EmreErbas/Meropeidae_Horologium/Documents/Notes/Pictures/ESP32-S3-Feather-Lyt.png

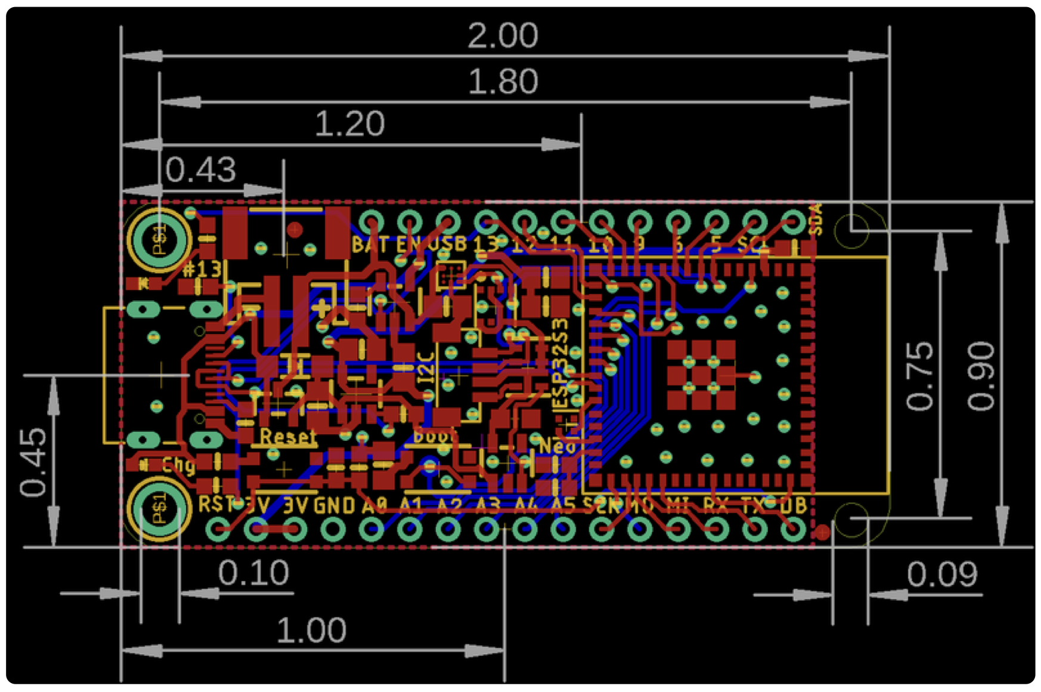
Documents/Notes/Pictures/ESP32-S3-Feather-Lyt.png
