EmreErbas/Meropeidae_Horologium/Documents/Notes/Pictures/Panel-Port-Down.png

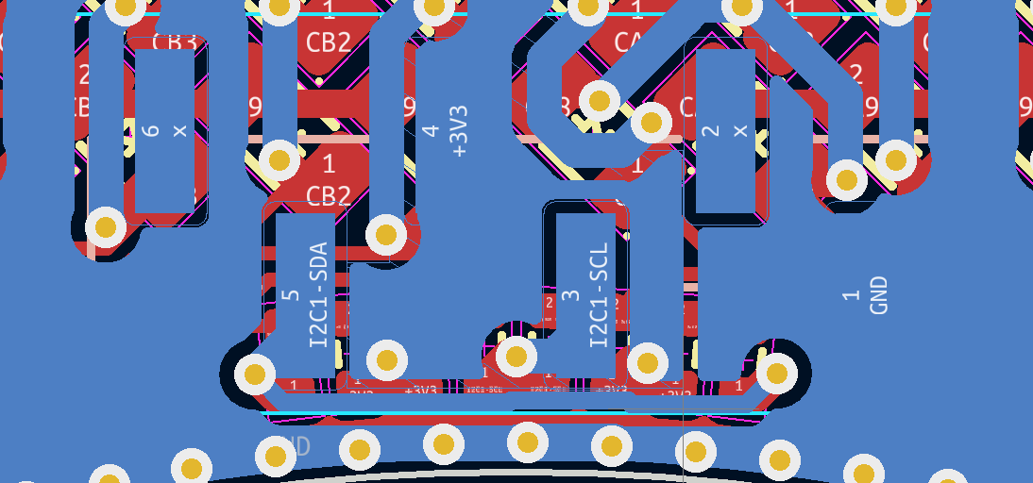
Documents/Notes/Pictures/Panel-Port-Down.png
