EmreErbas/Meropeidae_Horologium/Documents/Notes/Pictures/Panel-Port-Up.png

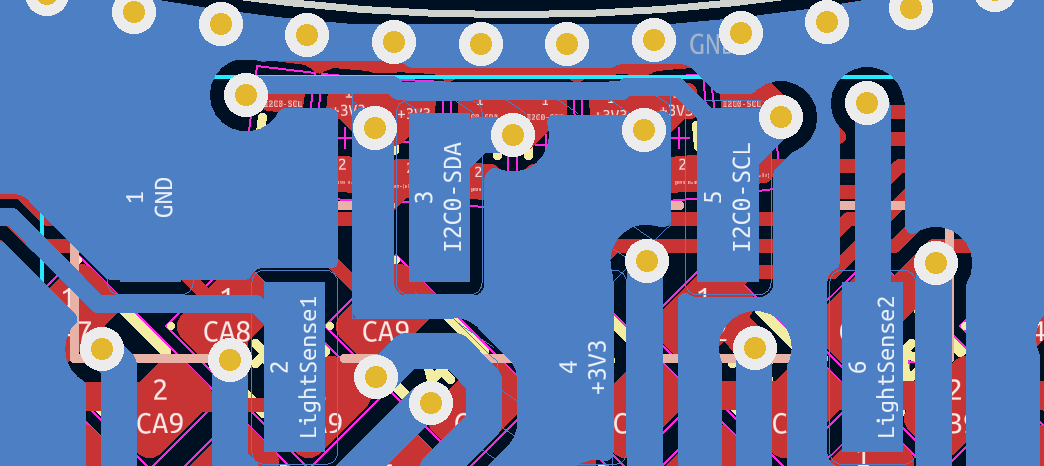
Documents/Notes/Pictures/Panel-Port-Up.png
